shotaro-sharkle1112/slingshot-controller/hardware/images/IMG_3019.jpg

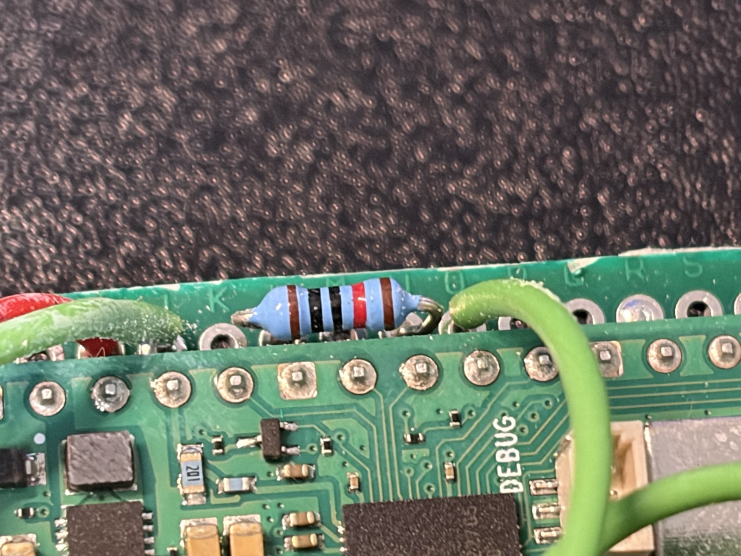
hardware/images/IMG_3019.jpg
